MAATHES-THILAK-K/Arduino-SMD/OPENSOURCE_REMAKE/IMAGES/ISOMETRIC.png

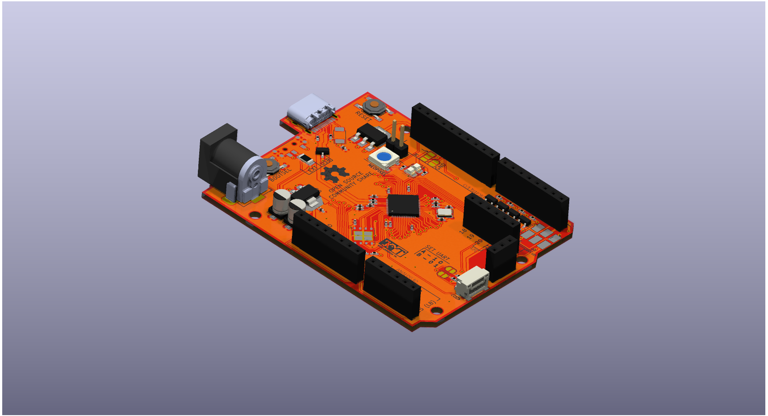
OPENSOURCE_REMAKE/IMAGES/ISOMETRIC.png
